rdb64-hobbies/Perceptron/assets/orient_led.jpg

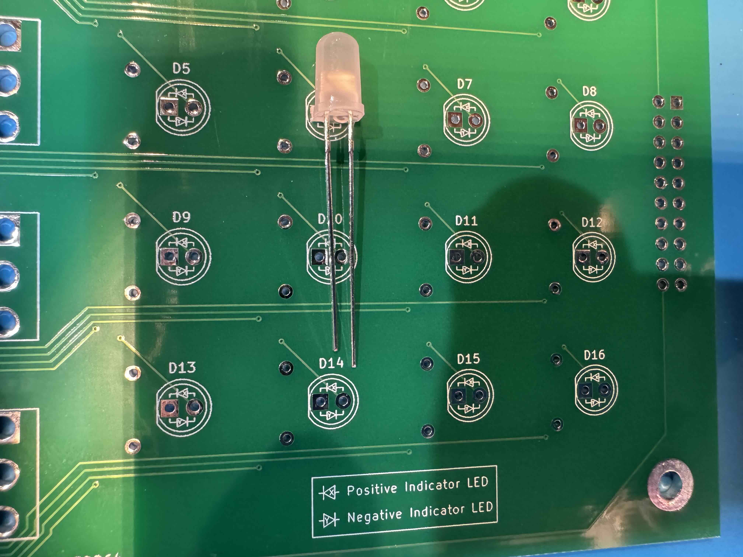
assets/orient_led.jpg
