rdb64-hobbies/Perceptron/assets/pcbs_front.jpg

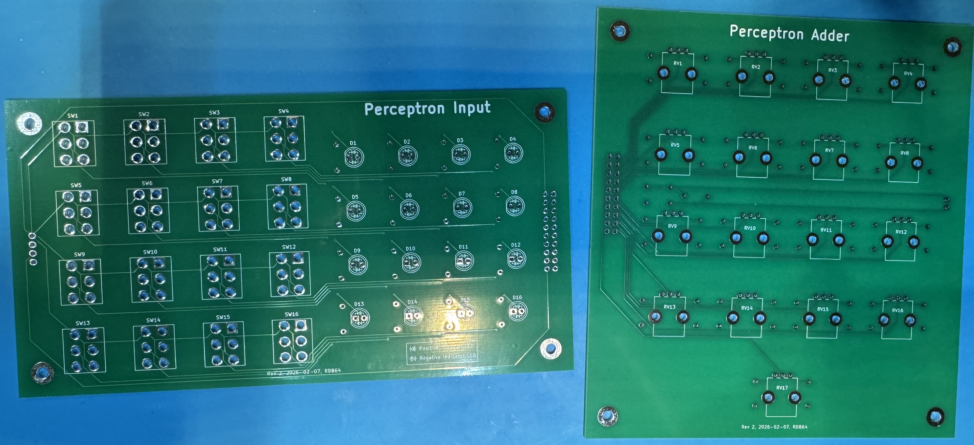
assets/pcbs_front.jpg
